Calvariaa/zkxh_robot_race_-foc_2025/mainboard_stm32g431/Core/Inc/icm42688.h

#ifndef __ICM42688_H
#define __ICM42688_H

#include "stm32g4xx_hal.h"

extern uint8_t dma_gyro_data[6];

// ICM-42688-P I2C地址 (AD0引脚低电平)
#define ICM42688_ADDRESS         0x68

// 寄存器地址 (Bank 0)
#define REG_BANK_SEL            0x76
#define WHO_AM_I                0x75
#define PWR_MGMT0               0x4E
#define GYRO_CONFIG0            0x4F
#define ACCEL_CONFIG0           0x50
#define DEVICE_CONFIG           0x11
#define INT_CONFIG              0x14
#define ACCEL_DATA_X1           0x1F
#define GYRO_DATA_X1            0x25
#define TEMP_DATA1              0x1D

// 错误代码
#define ICM42688_OK             0
#define ICM42688_ERR_INIT       1
#define ICM42688_ERR_COMM       2

// 函数声明
uint8_t ICM42688_Init(I2C_HandleTypeDef *hi2c);
uint8_t ICM42688_WhoAmI(I2C_HandleTypeDef *hi2c);
void ICM42688_Reset(I2C_HandleTypeDef *hi2c);
HAL_StatusTypeDef ICM42688_WriteReg(I2C_HandleTypeDef *hi2c, uint8_t reg, uint8_t value);
HAL_StatusTypeDef ICM42688_ReadReg(I2C_HandleTypeDef *hi2c, uint8_t reg, uint8_t *data, uint16_t len);
HAL_StatusTypeDef ICM42688_ReadAccel(I2C_HandleTypeDef *hi2c, int16_t accel[3]);
HAL_StatusTypeDef ICM42688_ReadGyro(I2C_HandleTypeDef *hi2c, int16_t gyro[3]);
void ICM42688_ReadGyro_DMA(int16_t gyro[3]);
float ICM42688_ReadTemperature(I2C_HandleTypeDef *hi2c);

#endif /* __ICM42688_H */
