Calvariaa/zkxh_robot_race_-foc_2025/mainboard_stm32g431/Core/Inc/mpu6050.h

/*
 * mpu6050.h
 *
 *  Created on: Nov 13, 2019
 *      Author: Bulanov Konstantin
 */

#ifndef INC_GY521_H_
#define INC_GY521_H_

#endif /* INC_GY521_H_ */

#include <stdint.h>
#include "i2c.h"

#define ANGLE_TO_RAD(x)     ( (x) * PI / 180.0 )                                // 角度转换为弧度
#define RAD_TO_ANGLE(x)     ( (x) * 180.0 / PI )                                // 弧度转换为角度
#define PI                  ( 3.1415926535898 )

// MPU6050 structure
typedef struct
{

    int16_t Accel_X_RAW;
    int16_t Accel_Y_RAW;
    int16_t Accel_Z_RAW;
    double Ax;
    double Ay;
    double Az;

    int16_t Gyro_X_RAW;
    int16_t Gyro_Y_RAW;
    int16_t Gyro_Z_RAW;
    double Gx;
    double Gy;
    double Gz;

    float Temperature;

    double KalmanAngleX;
    double KalmanAngleY;
} MPU6050_t;

// Kalman structure
typedef struct
{
    double Q_angle;
    double Q_bias;
    double R_measure;
    double angle;
    double bias;
    double P[2][2];
} Kalman_t;

extern MPU6050_t MPU6050;

uint8_t MPU6050_Init(I2C_HandleTypeDef *I2Cx);

void MPU6050_Read_Accel(I2C_HandleTypeDef *I2Cx, MPU6050_t *DataStruct);

void MPU6050_Read_Gyro(I2C_HandleTypeDef *I2Cx, MPU6050_t *DataStruct);

void MPU6050_Read_Temp(I2C_HandleTypeDef *I2Cx, MPU6050_t *DataStruct);

void MPU6050_Read_All(I2C_HandleTypeDef *I2Cx, MPU6050_t *DataStruct);

double Kalman_getAngle(Kalman_t *Kalman, double newAngle, double newRate, double dt);
