Calvariaa/zkxh_robot_race_-foc_2025/simplefoc_stm32g431/Core/Src/fast_foc.c

#include "fast_foc.h"

#include <math.h>
#include <stdlib.h>

#define FAST_FOC_ENCODER_MAX    (uint16_t)(65535)                                         // 定义默认磁编码器的最大值 最大支持 16位磁编码

#define FAST_FOC_POLE_PAIRS     (uint16_t)(7)                                             // 定义默认的电机极对数 通过极对数计算电角度

#define FAST_FOC_ARRAY_LENGTH   (uint16_t)(FAST_FOC_ENCODER_MAX / FAST_FOC_POLE_PAIRS)    // 定义查表数组长度 磁编码器最大值 / 极对数

#define FAST_FOC_PHASE_OFFSET   (uint16_t)(FAST_FOC_ARRAY_LENGTH / 3)                     // 定义相位偏差值 三相波形相差120度 

#define FAST_FOC_DUTY_MAX       (uint16_t)(10000)                                         // 定义输出的最大占空比

#define fast_foc_limit_ab(x, a, b)  ((x) < (a) ? (a) : ((x) > (b) ? (b) : (x)))         // FAST_FOC 宏定义限幅函数

#if     USE_SIN_DATA == 1
// 生成的 正弦波查表数组 
const uint16_t foc_output_array[FAST_FOC_ARRAY_LENGTH] = {
  5000, 5003, 5006, 5010, 5013, 5016, 5020, 5023, 5026, 5030, 5033, 5036, 5040, 5043, 5046, 5050,
  5053, 5057, 5060, 5063, 5067, 5070, 5073, 5077, 5080, 5083, 5087, 5090, 5093, 5097, 5100, 5104,
  5107, 5110, 5114, 5117, 5120, 5124, 5127, 5130, 5134, 5137, 5140, 5144, 5147, 5150, 5154, 5157,
  5161, 5164, 5167, 5171, 5174, 5177, 5181, 5184, 5187, 5191, 5194, 5197, 5201, 5204, 5207, 5211,
  5214, 5218, 5221, 5224, 5228, 5231, 5234, 5238, 5241, 5244, 5248, 5251, 5254, 5258, 5261, 5264,
  5268, 5271, 5275, 5278, 5281, 5285, 5288, 5291, 5295, 5298, 5301, 5305, 5308, 5311, 5315, 5318,
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
  7867, 7872, 7878, 7884, 7889, 7895, 7901, 7906, 7912, 7918, 7923, 7929, 7935, 7940, 7946, 7951,
  7957, 7963, 7968, 7974, 7979, 7985, 7991, 7996, 8002, 8007, 8013, 8018, 8024, 8029, 8035, 8040,
  8046, 8051, 8057, 8062, 8068, 8073, 8079, 8084, 8090, 8095, 8101, 8106, 8112, 8117, 8122, 8128,
  8133, 8139, 8144, 8149, 8155, 8160, 8165, 8171, 8176, 8181, 8187, 8192, 8197, 8203, 8208, 8213,
  8219, 8224, 8229, 8235, 8240, 8245, 8250, 8256, 8261, 8266, 8271, 8276, 8282, 8287, 8292, 8297,
  8302, 8308, 8313, 8318, 8323, 8328, 8333, 8339, 8344, 8349, 8354, 8359, 8364, 8369, 8374, 8379,
  8384, 8390, 8395, 8400, 8405, 8410, 8415, 8420, 8425, 8430, 8435, 8440, 8445, 8450, 8455, 8460,
  8465, 8470, 8475, 8479, 8484, 8489, 8494, 8499, 8504, 8509, 8514, 8519, 8524, 8528, 8533, 8538,
  8543, 8548, 8553, 8557, 8562, 8567, 8572, 8577, 8581, 8586, 8591, 8596, 8601, 8605, 8610, 8615,
  8619, 8624, 8629, 8634, 8638, 8643, 8648, 8652, 8657, 8662, 8666, 8671, 8676, 8680, 8685, 8689,
  8694, 8699, 8703, 8708, 8712, 8717, 8721, 8726, 8731, 8735, 8740, 8744, 8749, 8753, 8758, 8762,
  8767, 8771, 8776, 8780, 8784, 8789, 8793, 8798, 8802, 8807, 8811, 8815, 8820, 8824, 8828, 8833,
  8837, 8842, 8846, 8850, 8855, 8859, 8863, 8867, 8872, 8876, 8880, 8885, 8889, 8893, 8897, 8902,
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
};

#endif

fast_foc_struct motor_left_foc_driver; // 定义左侧电机的 FAST_FOC 结构体

fast_foc_struct motor_right_foc_driver; // 定义右侧电机的 FAST_FOC 结构体


void mos_init(TIM_HandleTypeDef *_htim) {
  HAL_TIM_PWM_Start(_htim,TIM_CHANNEL_1);
  HAL_TIM_PWM_Start(_htim,TIM_CHANNEL_2);
  HAL_TIM_PWM_Start(_htim,TIM_CHANNEL_3);

  HAL_TIMEx_PWMN_Start(_htim,TIM_CHANNEL_1);
  HAL_TIMEx_PWMN_Start(_htim,TIM_CHANNEL_2);
  HAL_TIMEx_PWMN_Start(_htim,TIM_CHANNEL_3);
}

void mos_all_set(const TIM_HandleTypeDef *_htim, const uint32_t _cmp_u, const uint32_t _cmp_v, const uint32_t _cmp_w) {
  __HAL_TIM_SET_COMPARE(_htim, TIM_CHANNEL_3, _cmp_u);
  __HAL_TIM_SET_COMPARE(_htim, TIM_CHANNEL_2, _cmp_v);
  __HAL_TIM_SET_COMPARE(_htim, TIM_CHANNEL_1, _cmp_w);
}

void mos_all_close(const TIM_HandleTypeDef *_htim) {
  mos_all_set(_htim, 0, 0, 0);
}


//-------------------------------------------------------------------------------------------------------------------
// 函数简介     FAST_FOC 查表计算函数
// 参数说明     fast_foc_pointer      FAST_FOC 参数结构体
// 参数说明     now_encoder_data      当前的磁编码器数值  无需处理 原始数据即可
// 参数说明     output_duty_max       当前需要输出的占空比
// 参数说明     traction_angle        当前的牵引角度
// 返回参数     void
// 使用示例     fast_foc_calculate(&motor_left_foc_driver,                                  // FAST-FOC 计算 三相输出值
//                                  motor_left.menc15a_value_now,
//                                  motor_left.motor_duty > 0 ? motor_left.motor_duty : -motor_left.motor_duty,
//                                  motor_left.motor_duty > 0 ? motor_left.motor_control_angle : -motor_left.motor_control_angle);
// 备注信息
//-------------------------------------------------------------------------------------------------------------------
void foc_control_fast(fast_foc_struct *fast_foc_pointer, int32_t now_encoder_data, float output_uq) {
  register int32_t encoder_temp asm("r0"); // 定义磁编码器数据临时变量

  int32_t location_temp_a = 0; // 定义三相输出位置临时变量
  int32_t location_temp_b = 0;
  int32_t location_temp_c = 0;

  float output_duty_max = fabsf(output_uq);

  if (fast_foc_pointer->motor_rotation_direction == 1) // 如果方向为反向 则将编码器数据也反相
  {
    now_encoder_data = fast_foc_pointer->encoder_max_data - now_encoder_data;
  }

  fast_foc_pointer->encoder_now_data = now_encoder_data;

  int32_t d_angle = fast_foc_pointer->encoder_now_data - fast_foc_pointer->encoder_last_data;
  if (abs(d_angle) > (int32_t) (0.8f * fast_foc_pointer->encoder_max_data))
    fast_foc_pointer->rotate += (d_angle > 0) ? -1 : 1;

  fast_foc_pointer->speed_raw = d_angle + (fast_foc_pointer->rotate - fast_foc_pointer->rotate_last) * fast_foc_pointer
                                ->encoder_max_data;

  fast_foc_pointer->rotate_last = fast_foc_pointer->rotate;
  fast_foc_pointer->encoder_last_data = fast_foc_pointer->encoder_now_data;

  // 1ms算一次
  fast_foc_pointer->speed_actual_sum += fast_foc_pointer->speed_raw;
  if (++fast_foc_pointer->speed_calc_time >= PWM_FREQUENCY / 1000) {
    fast_foc_pointer->speed_calc_time = 0;

    fast_foc_pointer->speed_filtered = (
        8 * fast_foc_pointer->speed_actual_sum +
        2 * fast_foc_pointer->speed_actual_result) / 10;
    fast_foc_pointer->speed_actual_result = fast_foc_pointer->speed_actual_sum;
    fast_foc_pointer->speed_actual_sum = 0;
  }



  const uint8_t preact_angle = (uint8_t) (func_limit_ab(
    (abs(fast_foc_pointer->speed_filtered) / (FOC_MOTOR_KV_NUM * 12.0f)), 0.0f,
    1.0f) * (float) fast_foc_pointer->preact_angle);

  // const uint8_t preact_angle = 30;

  encoder_temp = (now_encoder_data - fast_foc_pointer->motor_zero_location - fast_foc_pointer->calculate_value.
                  encoder_pole_pairs *
                  (output_uq > 0
                     ? (fast_foc_pointer->traction_angle - preact_angle)
                     : -(fast_foc_pointer->traction_angle - preact_angle)
                  ) / 360 + fast_foc_pointer->encoder_max_data)
                 % fast_foc_pointer->encoder_max_data; // 拟合位置   当前编码器位置 - 零点 + 牵引角


  encoder_temp = encoder_temp % fast_foc_pointer->calculate_value.encoder_pole_pairs; // 计算电角度位置

  encoder_temp = (uint32_t) ((float) encoder_temp / fast_foc_pointer->calculate_value.encoder_proportion);
  // 计算编码器数据缩放 实际值缩放到查表的大小

  location_temp_a = (int32_t) encoder_temp; // 获取A相查表位置

  location_temp_b = (int32_t) (encoder_temp - FAST_FOC_PHASE_OFFSET + FAST_FOC_ARRAY_LENGTH) % FAST_FOC_ARRAY_LENGTH;
  // 获取B相查表位置

  location_temp_c = (int32_t) (encoder_temp + FAST_FOC_PHASE_OFFSET + FAST_FOC_ARRAY_LENGTH) % FAST_FOC_ARRAY_LENGTH;
  // 获取C相查表位置

  fast_foc_pointer->ouput_duty[0] = (uint16_t) (
    (float) (foc_output_array[location_temp_a] - 5000) * fast_foc_pointer->
    calculate_value.duty_proportion *
    output_duty_max + PWM_COUNT_PERIOD / 2); // A相占空比缩放并限幅

  fast_foc_pointer->ouput_duty[1] = (uint16_t) (
    (float) (foc_output_array[location_temp_b] - 5000) * fast_foc_pointer->
    calculate_value.duty_proportion *
    output_duty_max + PWM_COUNT_PERIOD / 2); // B相占空比缩放并限幅

  fast_foc_pointer->ouput_duty[2] = (uint16_t) (
    (float) (foc_output_array[location_temp_c] - 5000) * fast_foc_pointer->
    calculate_value.duty_proportion *
    output_duty_max + PWM_COUNT_PERIOD / 2); // C相占空比缩放并限幅

  mos_all_set(fast_foc_pointer->htim, fast_foc_pointer->ouput_duty[0], fast_foc_pointer->ouput_duty[1],
              fast_foc_pointer->ouput_duty[2]);
}


//-------------------------------------------------------------------------------------------------------------------
// 函数简介     FAST_FOC 初始化函数
// 参数说明     fast_foc_pointer      FAST_FOC 参数结构体
// 参数说明     encoder_max_data      当前的磁编码器的采样最大值 比如15位精度 则填写 32767
// 参数说明     duty_max_data         当前定时器输出的三相PWM最大周期
// 参数说明     motor_pole_pairs      当前电机的极对数
// 参数说明     zero_location         当前电机的零点位置
// 参数说明     rotation_direction    当前电机的旋转方向
// 返回参数     void
// 使用示例     fast_foc_init(&motor_right_foc_driver, ENCODER_PRECISION, OUTPUT_DUTY_MAX, motor_left.pole_pairs,  motor_left.zero_location,  motor_left.rotation_direction );     // 左侧电机 FAST_FOC 功能初始化
// 备注信息
//-------------------------------------------------------------------------------------------------------------------
void foc_control_fast_init(TIM_HandleTypeDef *htim, fast_foc_struct *fast_foc_pointer, int32_t encoder_max_data,
                           int32_t duty_max_data, uint32_t motor_pole_pairs, int32_t zero_location,
                           int32_t rotation_direction, int16_t traction_angle, int16_t preact_angle) {
  fast_foc_pointer->htim = htim;

  fast_foc_pointer->encoder_max_data = encoder_max_data; // 保存当前磁编码器的最大值

  fast_foc_pointer->duty_max_data = duty_max_data; // 保存当前输出占空比的最大值

  fast_foc_pointer->motor_pole_pairs = motor_pole_pairs; // 保存当前电机的极对数

  fast_foc_pointer->motor_zero_location = zero_location; // 保存当前电机的零点位置

  fast_foc_pointer->motor_rotation_direction = rotation_direction; // 保存当前电机的旋转方向

  fast_foc_pointer->traction_angle = traction_angle;

  fast_foc_pointer->preact_angle = preact_angle;

  fast_foc_pointer->calculate_value.encoder_pole_pairs = encoder_max_data / motor_pole_pairs;
  // 计算当前电机一圈电角度对应的磁编码器数值范围

  fast_foc_pointer->calculate_value.encoder_proportion =
      (float) fast_foc_pointer->calculate_value.encoder_pole_pairs / (float) FAST_FOC_ARRAY_LENGTH;
  // 计算当前电机一圈电角度对应查表数组的缩放比例

  fast_foc_pointer->calculate_value.duty_proportion = (float) duty_max_data / (float) FAST_FOC_DUTY_MAX;
  // 计算当前电机的最大占空比与查表数组的缩放比例
}
